Makerfabs/ESP32S3_4.2_EINK/example/pic_display_web/2.bmp

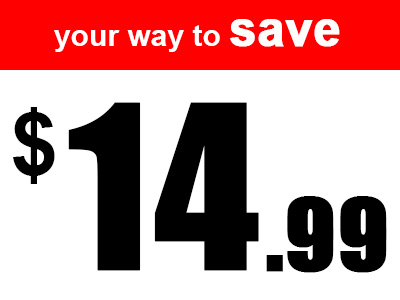
example/pic_display_web/2.bmp
